Leoruiz197/cofre_FIAP_V2/STLs/fiap1.stl

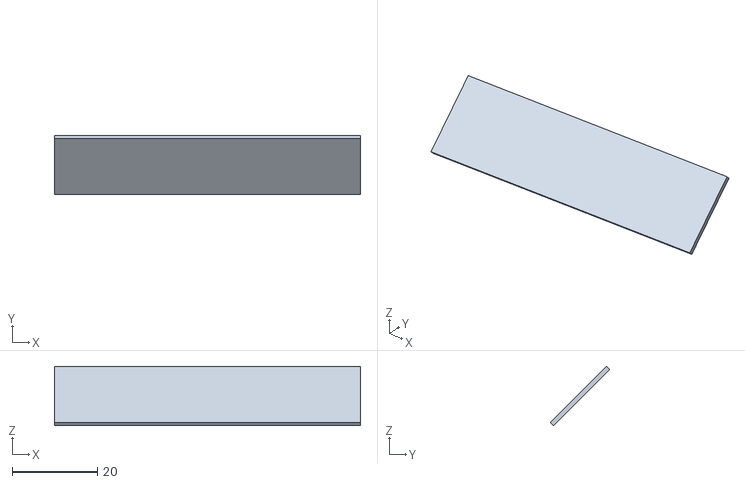
[picture p16: CAD file, 2026-05-05]
STLs/fiap1.stl
72.0 x 14.0 x 14.0
