Leoruiz197/cofre_FIAP_V2/STLs/iris/led1.stl

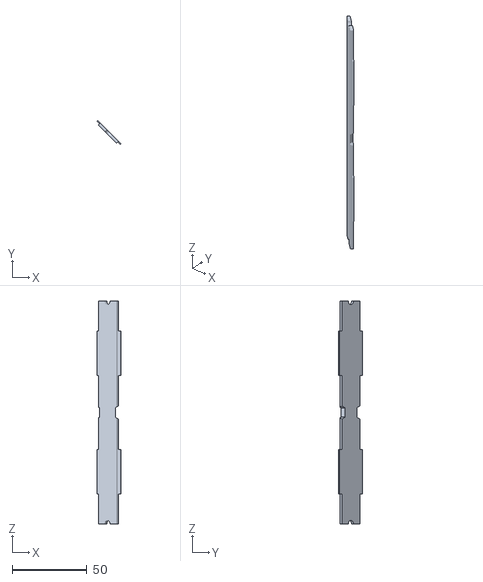
[picture p18: CAD file, 2026-05-05]
STLs/iris/led1.stl
16.2 x 16.2 x 149.4
