Leoruiz197/cofre_FIAP_V2/STLs/t2.stl

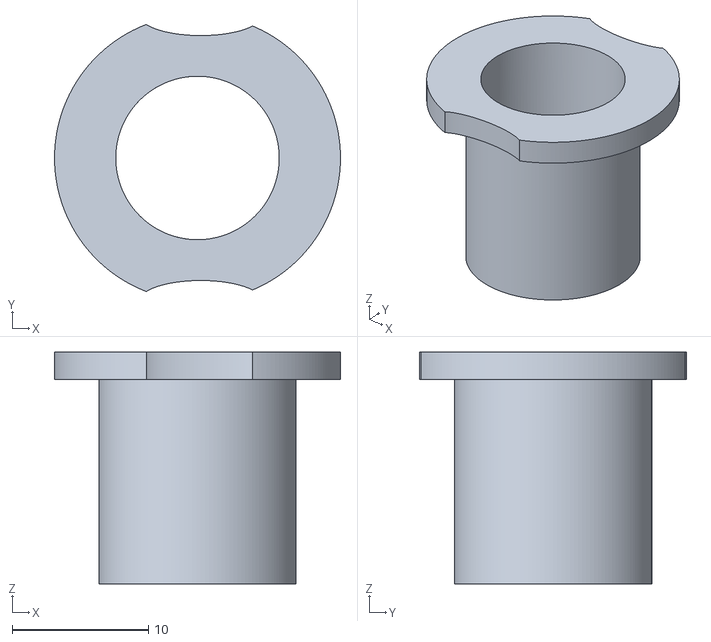
[picture p19: CAD file, 2026-05-05]
STLs/t2.stl
21.0 x 19.6 x 17.0
