Leoruiz197/cofre_FIAP_V2/STLs/Corpo145.stl

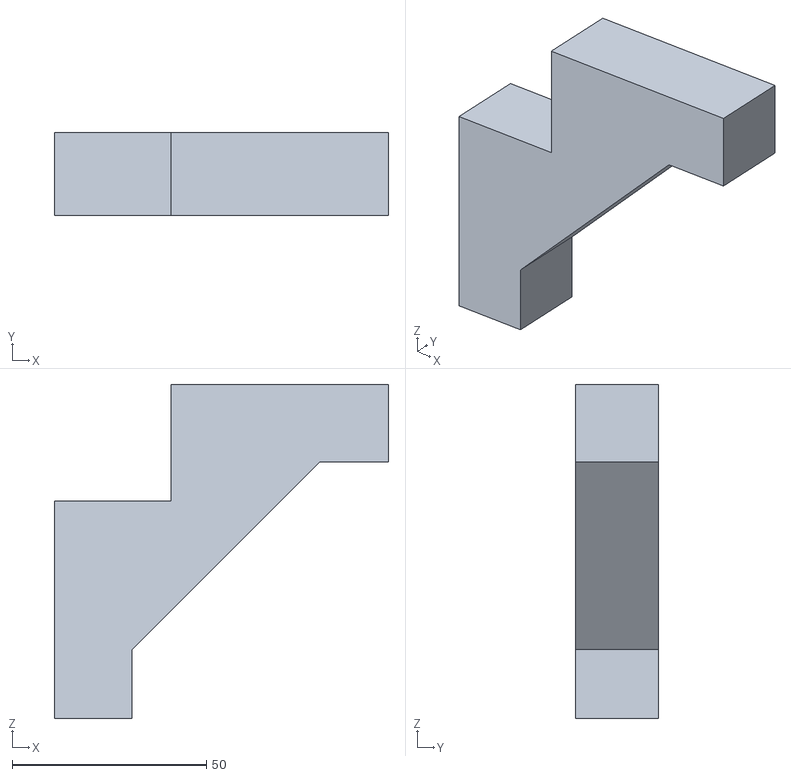
[picture p21: CAD file, 2026-05-05]
STLs/Corpo145.stl
86.0 x 21.5 x 86.0
