Leoruiz197/cofre_FIAP_V2/STLs/iris/base iris.stl

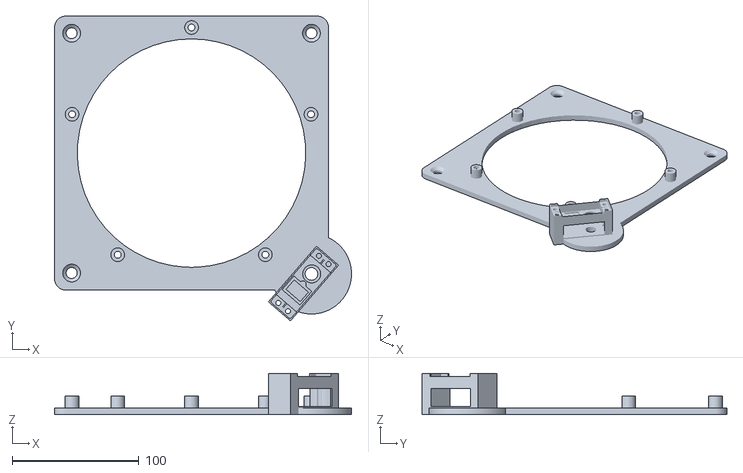
[picture p22: CAD file, 2026-05-05]
STLs/iris/base iris.stl
234.1 x 240.3 x 32.6
