Leoruiz197/cofre_FIAP_V2/STLs/2d/1.dxf

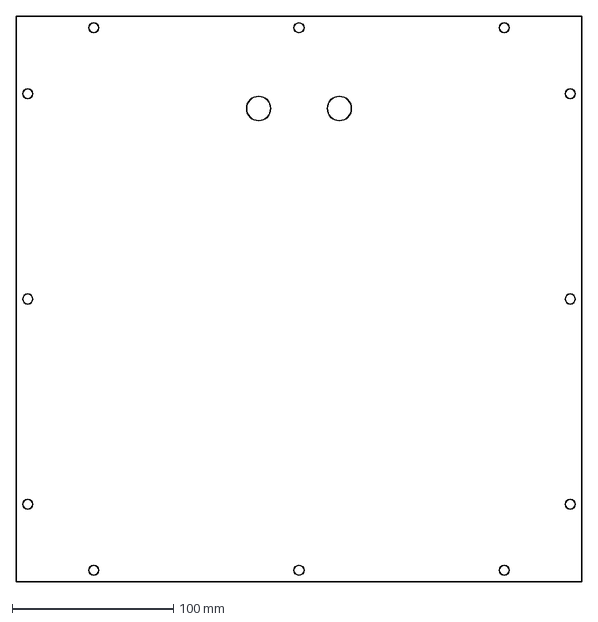
[picture p23: CAD file, 2026-05-05]
STLs/2d/1.dxf
350.0 x 350.0 mm
