Leoruiz197/cofre_FIAP_V2/STLs/4.stl

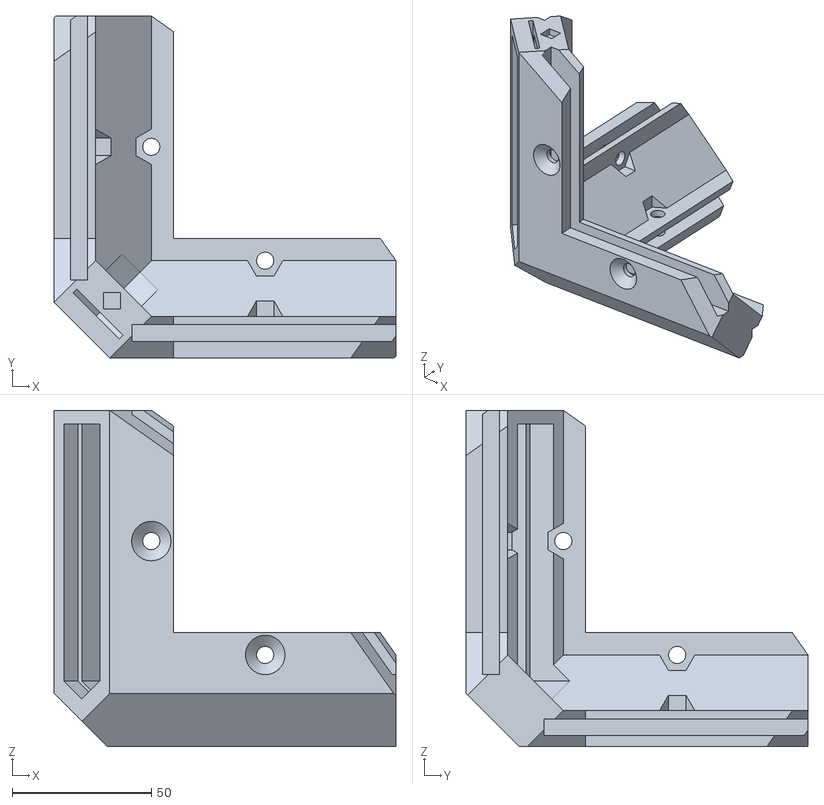
[picture p24: CAD file, 2026-05-05]
STLs/4.stl
123.0 x 123.0 x 121.0
