Leoruiz197/cofre_FIAP_V2/STLs/iris/Petg1.stl

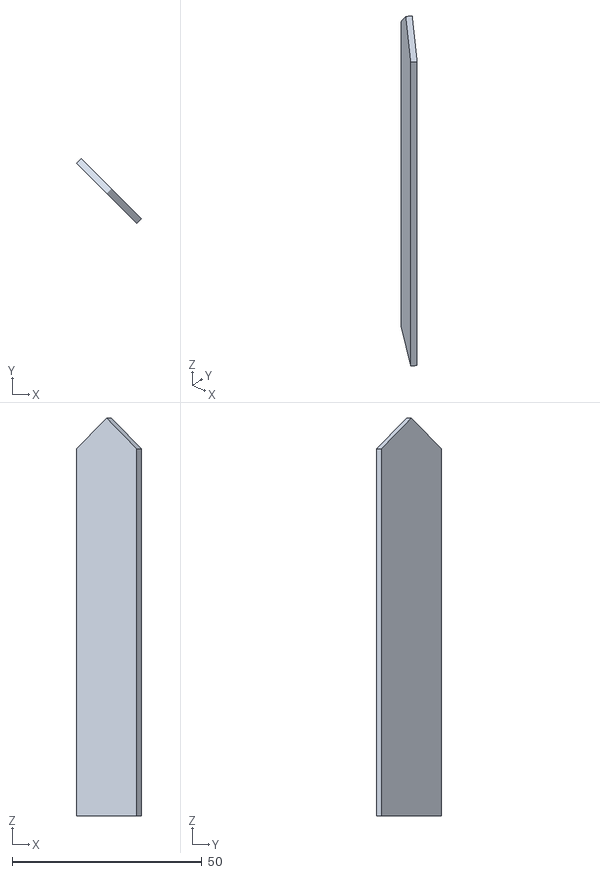
[picture p25: CAD file, 2026-05-05]
STLs/iris/Petg1.stl
17.2 x 17.2 x 104.8
