Leoruiz197/cofre_FIAP_V2/STLs/2d/8.dxf

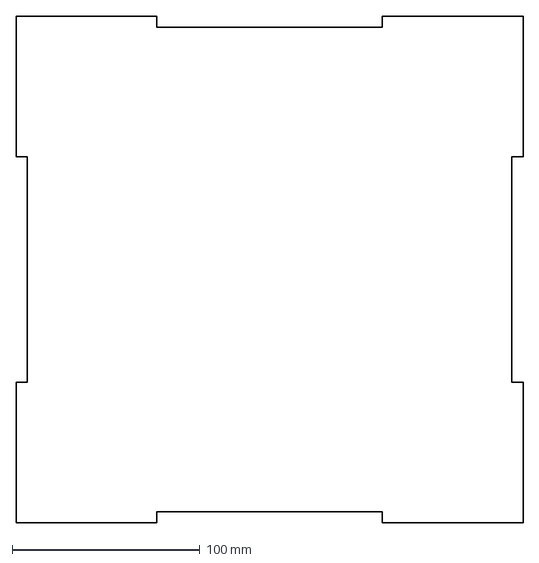
[picture p26: CAD file, 2026-05-05]
STLs/2d/8.dxf
270.0 x 270.0 mm
