Leoruiz197/cofre_FIAP_V2/STLs/2d/gui2.dxf

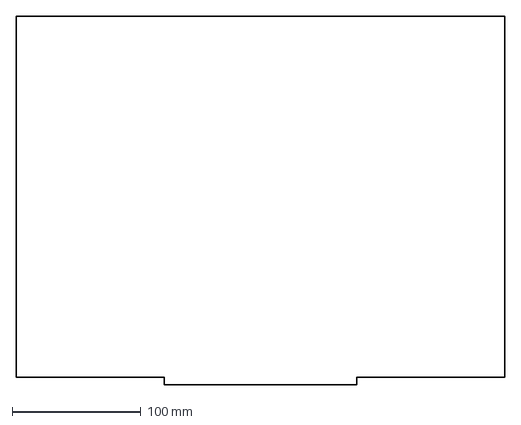
[picture p27: CAD file, 2026-05-05]
STLs/2d/gui2.dxf
380.0 x 286.7 mm
