Leoruiz197/cofre_FIAP_V2/STLs/engrenagem grande.stl

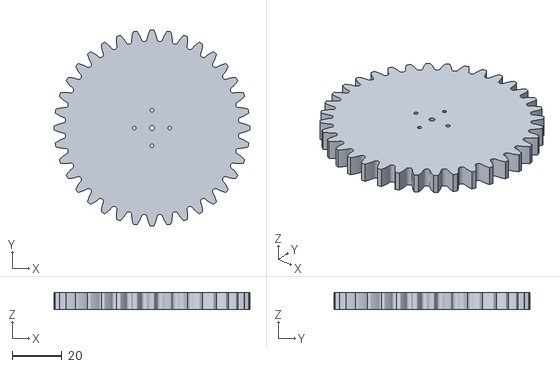
[picture p28: CAD file, 2026-05-05]
STLs/engrenagem grande.stl
79.0 x 79.0 x 6.93
