Leoruiz197/cofre_FIAP_V2/STLs/altofalante.stl

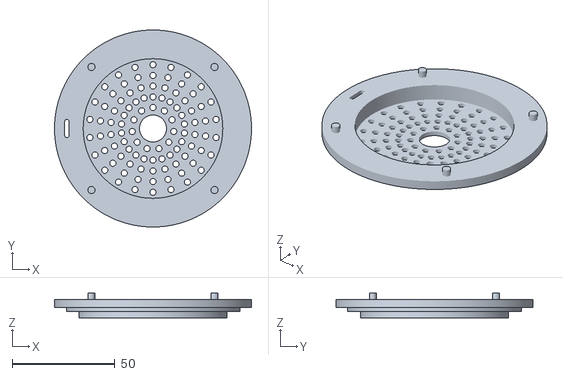
[picture p29: CAD file, 2026-05-05]
STLs/altofalante.stl
96.0 x 96.0 x 12.0
