Leoruiz197/cofre_FIAP_V2/STLs/iris/baseplate-aperature.stl.stl

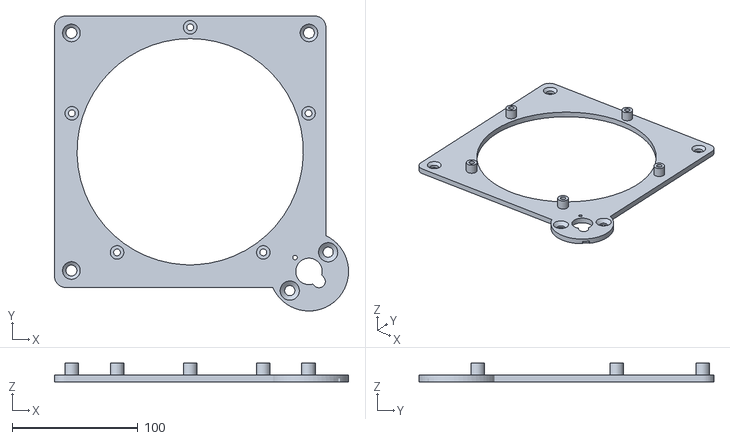
[picture p30: CAD file, 2026-05-05]
STLs/iris/baseplate-aperature.stl.stl
234.0 x 234.7 x 14.8
