Leoruiz197/cofre_FIAP_V2/STLs/3.stl

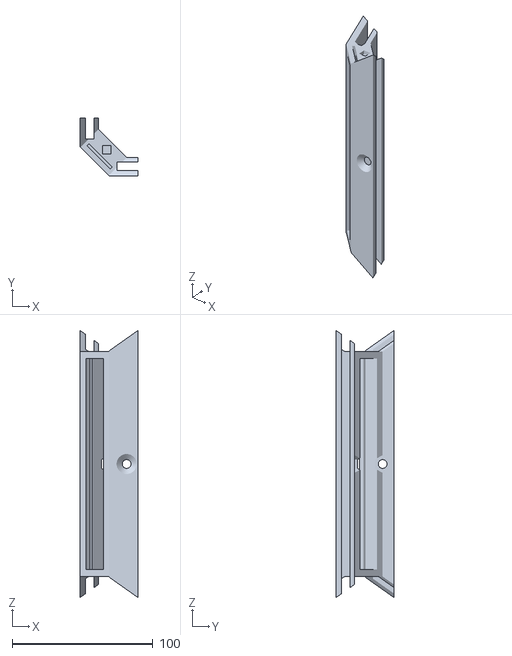
[picture p31: CAD file, 2026-05-05]
STLs/3.stl
41.0 x 41.0 x 189.4
