Leoruiz197/cofre_FIAP_V2/STLs/iris/iris.stl

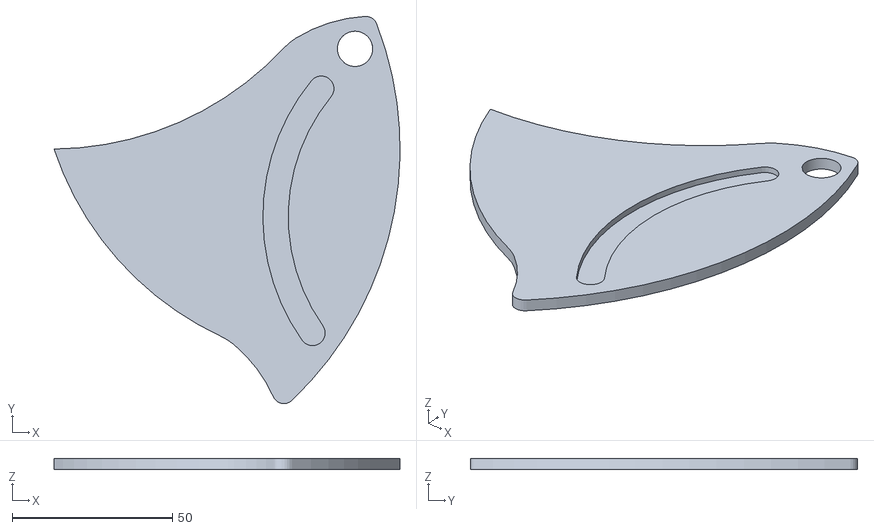
[picture p32: CAD file, 2026-05-05]
STLs/iris/iris.stl
108.0 x 120.9 x 3.50
