Leoruiz197/cofre_FIAP_V2/STLs/Corpo de malha1.stl

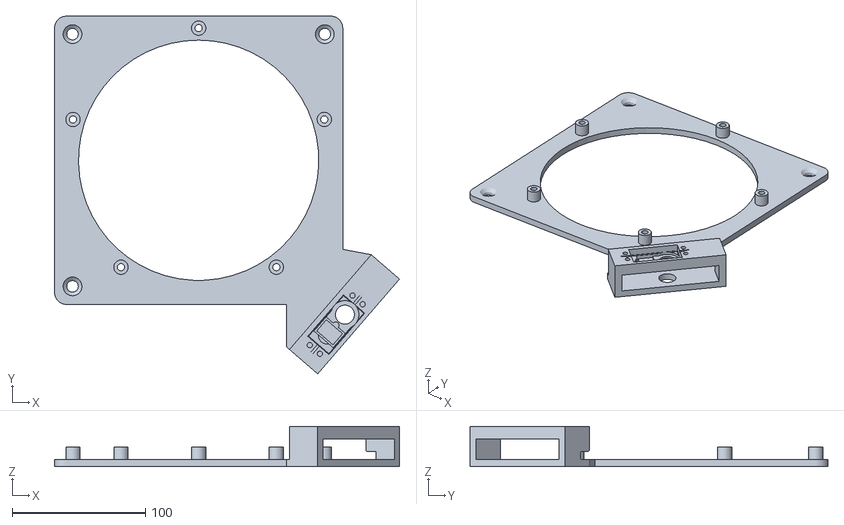
[picture p33: CAD file, 2026-05-05]
STLs/Corpo de malha1.stl
258.5 x 268.0 x 30.0
