Leoruiz197/cofre_FIAP_V2/STLs/apoio.stl

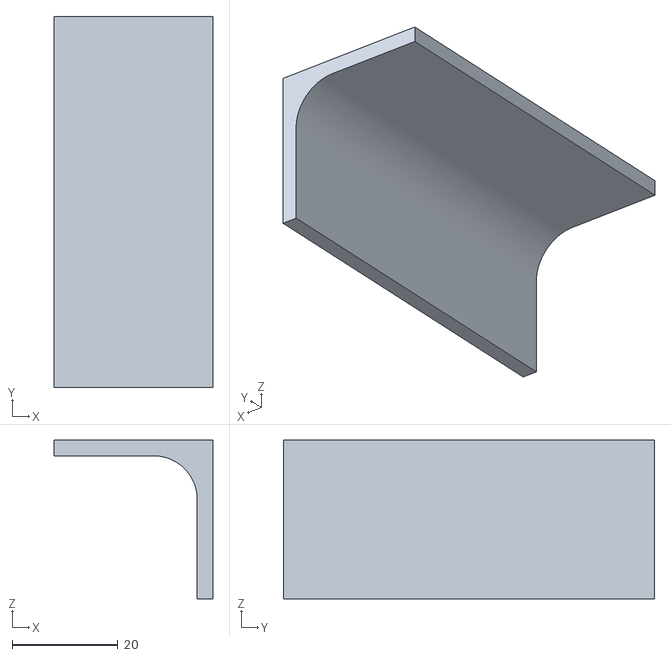
[picture p34: CAD file, 2026-05-05]
STLs/apoio.stl
30.0 x 70.0 x 30.0
