Leoruiz197/cofre_FIAP_V2/STLs/iris/petg2.stl

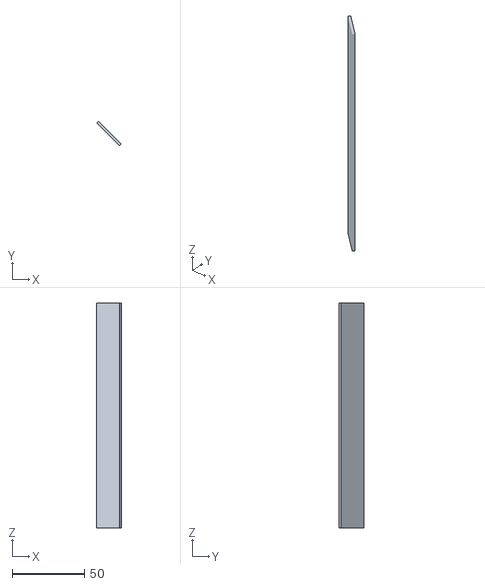
[picture p35: CAD file, 2026-05-05]
STLs/iris/petg2.stl
17.2 x 17.2 x 156.2
