Leoruiz197/cofre_FIAP_V2/src/tasks/websocket_task.cpp

#include <Arduino.h>
#include <ArduinoJson.h>
#include <WiFi.h>
#include <freertos/FreeRTOS.h>
#include <freertos/task.h>
#include "websocket_task.h"
#include "../websocket.h"
#include "../system_state.h"
#include "../hardware.h"
#include "../dfplayer.h"

extern TaskHandle_t mpuTaskHandle;

unsigned long lastWsReconnectAttempt = 0;

void webSocketEvent(WStype_t type, uint8_t * payload, size_t length);

void connectWebSocket() {
    int port = atoi(ws_port);

    if (port == 443) {
        Serial.println("[WS] Conectando com SSL");
        webSocket.beginSSL(ws_host, port, "/");
    } else {
        Serial.println("[WS] Conectando sem SSL");
        webSocket.begin(ws_host, port, "/");
    }

    webSocket.onEvent(webSocketEvent);
    webSocket.setReconnectInterval(5000);
    webSocket.enableHeartbeat(15000, 3000, 2);
}

void webSocketEvent(WStype_t type, uint8_t * payload, size_t length) {

    switch(type) {

        case WStype_CONNECTED:
            Serial.println("[WS] Conectado");
            wsConnected = true;
            lastWsReconnectAttempt = millis();

            // 🔥 envia identificação do device
            {
                JsonDocument doc;
                doc["device"] = device_id;

                String msg;
                serializeJson(doc, msg);

                webSocket.sendTXT(msg);
            }

            break;

        case WStype_DISCONNECTED:
            Serial.println("[WS] Desconectado");
            wsConnected = false;
            lastWsReconnectAttempt = millis();
            break;

        case WStype_ERROR:
            Serial.println("[WS] Erro na conexão");
            wsConnected = false;
            lastWsReconnectAttempt = millis();
            break;

        case WStype_TEXT:
            Serial.println("[WS] Mensagem recebida:");
            String msg = String((char*)payload);
            Serial.println(msg);

            JsonDocument doc;
            deserializeJson(doc, msg);

            String type = doc["type"];

            if (type == "batch") {

                JsonArray commands = doc["commands"];

                for (JsonObject cmd : commands) {

                    String command = cmd["command"];



                    // ================= SERVO =================
                    if (command == "LOCK") {

                        // tenta ler como string OU número
                        String action = cmd["value"] | "";

                        Serial.println("[CMD] LOCK:");
                        Serial.println(action);

                        // ✔ modo OPEN / CLOSE
                        if (action == "OPEN") {
                            setDoorOpen();
                        }
                        else if (action == "CLOSE") {
                            setDoorClose();
                        }

                        // ✔ modo ANGLE (quando vier número)
                        else {

                            int angle = cmd["value"] | -1;

                            if (angle >= 0) {
                                Serial.print("[SERVO] Angulo direto: ");
                                Serial.println(angle);

                                setServo(angle);
                            }
                            else {
                                Serial.println("[LOCK] Valor inválido");
                            }
                        }
                    }

                    if (command == "SET_SERVO") {
                        int open = cmd["open"] | doorOpenAngle;
                        int close = cmd["close"] | doorCloseAngle;

                        saveServoAngles(open, close);

                        Serial.println("[CMD] SET_SERVO:");
                        Serial.print("Open: ");
                        Serial.println(doorOpenAngle);
                        Serial.print("Close: ");
                        Serial.println(doorCloseAngle);
                    }

                    // ================= LED =================
                    if (command == "LED") {

                        String target = cmd["target"] | "";

                        int r = cmd["r"] | 0;
                        int g = cmd["g"] | 0;
                        int b = cmd["b"] | 0;

                        Serial.println("[CMD] LED:");
                        Serial.print("Target: "); Serial.println(target);
                        Serial.print("RGB: ");
                        Serial.print(r); Serial.print(", ");
                        Serial.print(g); Serial.print(", ");
                        Serial.println(b);

                        if (target == "STRIP1") {
                            setLED1(r, g, b); // 🔥 chama hardware
                        }
                        if (target == "STRIP2") {
                            setLED2(r, g, b); // 🔥 chama hardware
                        }
                    }

                    if (command == "LEDS_OFF") {
                        Serial.println("[CMD] LEDS_OFF");

                        setLED1(0, 0, 0);
                        //setLED2(0, 0, 0);
                    }

                    // ================= LED Interno =================
                    if (command == "LED_INTERNAL") {
                        bool state = false;

                        if (cmd["value"].is<bool>()) {
                            state = cmd["value"].as<bool>();
                        } else if (cmd["value"].is<int>()) {
                            state = cmd["value"].as<int>() == 1;
                        } else if (cmd["value"].is<const char*>()) {
                            String value = cmd["value"].as<const char*>();
                            state = value == "1" || value == "true" || value == "ON";
                        }

                        Serial.println("[CMD] LED_INTERNAL:");
                        Serial.println(state);

                        luzInterno(state);
                    }

                    // ================= SMOKE =================
                    if (command == "SMOKE") {
                        bool state = false;

                        if (cmd["value"].is<bool>()) {
                            state = cmd["value"].as<bool>();
                        } else if (cmd["value"].is<int>()) {
                            state = cmd["value"].as<int>() == 1;
                        } else if (cmd["value"].is<const char*>()) {
                            String value = cmd["value"].as<const char*>();
                            state = value == "1" || value == "true" || value == "ON";
                        }

                        Serial.println("[CMD] SMOKE:");
                        Serial.println(state);

                        setSmoke(state);
                    }

                    if (command == "MOTION_SENSOR") {
                        bool state = true;

                        if (cmd["value"].is<bool>()) {
                            state = cmd["value"].as<bool>();
                        } else if (cmd["value"].is<int>()) {
                            state = cmd["value"].as<int>() == 1;
                        } else if (cmd["value"].is<const char*>()) {
                            String value = cmd["value"].as<const char*>();
                            state = value == "1" || value == "true" || value == "ON";
                        }

                        motionSensorEnabled = state;

                        Serial.println("[CMD] MOTION_SENSOR:");
                        Serial.println(motionSensorEnabled ? "ON" : "OFF");
                    }

                    // ================= SOUND =================
                    if (command == "SOUND") {
                        String action = cmd["action"] | "";

                        Serial.println("[CMD] SOUND:");
                        Serial.println(action);

                        if (action == "PLAY") {
                            int track = cmd["track"] | 1;
                            playSound(track);
                        }

                        else if (action == "STOP") {
                            stopSound();
                        }

                        else if (action == "SET_VOLUME") {
                            int volume = cmd["value"] | 20;

                            Serial.print("[CMD] Volume recebido: ");
                            Serial.println(volume);

                            setVolume(volume);
                        }

                        else if (action == "UP") {
                            volumeUp();
                        }

                        else if (action == "DOWN") {
                            volumeDown();
                        }
                    }

                    // ================= WIN EFFECT =================
                    if (command == "WIN_EFFECT") {

                        if (mpuTaskHandle != NULL) {
                            vTaskSuspend(mpuTaskHandle);
                        }
                        Serial.println("[CMD] WIN_EFFECT");
                        setLED1(0, 255, 0); 
                        playSound(random(5, 9)); // som 5 a 8

                        setSmoke(true);
                        delay(2000);

                        luzInterno(true);
                        
                        delay(500);
                        setDoorOpen();
                        
                        delay(5000);
                        setSmoke(false);
                        
                        if (mpuTaskHandle != NULL) {
                            vTaskResume(mpuTaskHandle);
                        }
                    }

                    // ================= ERROR EFFECT =================
                    if (command == "ERROR_EFFECT") {

                        Serial.println("[CMD] ERROR_EFFECT");

                        playSound(10);
                        int prevR = strip1R;
                        int prevG = strip1G;
                        int prevB = strip1B;

                        setLED1(255, 0, 0); // vermelho
                        delay(300);
                        setLED1(prevR, prevG, prevB);   // volta
                    }

                    // ================= RESET EFFECT =================
                    if (command == "RESET_EFFECT") {
                        Serial.println("[CMD] RESET_EFFECT");
                        setLED1(0, 0, 0); 
                        setSmoke(false);
                        luzInterno(false);
                        setDoorClose();

                        for (int i = 0; i < 3; i++) {
                            setLED1(255, 0, 0);
                            delay(150);
                            setLED1(0, 0, 0);
                            delay(150);
                        }
                    }
                }
            }
            break;
    }
}

void websocketTask(void *pvParameters) {

    Serial.println("[WS] Iniciando...");

    while (true) {

        // ================= GARANTE WIFI =================
        if (!wifiReady) {
            Serial.println("[WS] Aguardando WiFi...");
            vTaskDelay(2000 / portTICK_PERIOD_MS);
            continue;
        }

        // ================= TESTA DNS =================
        IPAddress ip;

        if (!WiFi.hostByName(ws_host, ip)) {
            Serial.println("[WS] DNS falhou, tentando novamente...");
            vTaskDelay(2000 / portTICK_PERIOD_MS);
            continue;
        }

        Serial.println("[WS] DNS OK, conectando...");

        // ================= CONECTA =================
        connectWebSocket();
        lastWsReconnectAttempt = millis();

        // ================= LOOP =================
        while (WiFi.status() == WL_CONNECTED) {
            webSocket.loop();

            if (!wsConnected && millis() - lastWsReconnectAttempt > 5000) {
                Serial.println("[WS] Forçando reconexão WebSocket...");
                lastWsReconnectAttempt = millis();
                webSocket.disconnect();
                connectWebSocket();
            }

            vTaskDelay(10 / portTICK_PERIOD_MS);
        }

        // se caiu WiFi, volta pro início
        Serial.println("[WS] WiFi caiu, reiniciando conexão...");
        wsConnected = false;

        vTaskDelay(2000 / portTICK_PERIOD_MS);
    }
}
