Leoruiz197/cofre_FIAP_V2/src/websocket.cpp

#include "websocket.h"
#include "./system_state.h"

WebSocketsClient webSocket;

void wsSend(String msg) {
    if (!wsConnected) return;
    webSocket.sendTXT(msg);
}

void wsInit(const char* host, int port) {
    webSocket.beginSSL(host, port, "/");
    //webSocket.begin(host, port, "/");
    webSocket.setReconnectInterval(5000);
}

void wsLoop() {
    webSocket.loop();
}
