Leoruiz197/cofre_FIAP_V2/src/dfplayer.h

#pragma once

#include <HardwareSerial.h>
#include <DFRobotDFPlayerMini.h>

extern HardwareSerial dfSerial;
extern DFRobotDFPlayerMini dfPlayer;

void playSound(int track);
void stopSound();
void initDFPlayer();

void setVolume(int volume);
void volumeUp();
void volumeDown();
